maaakit/GTIA2DVI/doc/img/calib_1.png

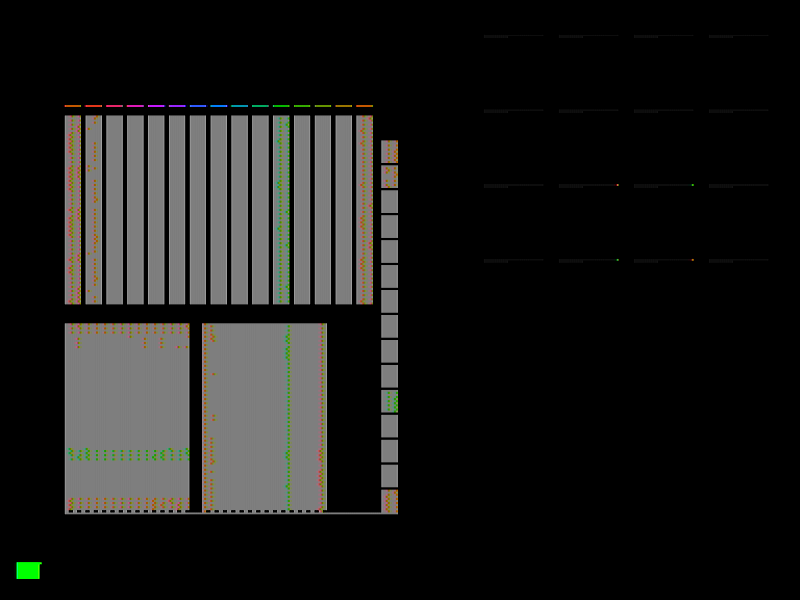
doc/img/calib_1.png
