maaakit/GTIA2DVI/software/gtia2dvi/gtia_palette.h

#include <stdlib.h>

#ifndef GTIA_PALETTE_H
#define GTIA_PALETTE_H

// PAL GTIA uses colors indexes 0-239 because color 15 is equal to color 1
// colors with indexes 240 to 255 are rgb colors used for example in menu screen

#define PALETTE_SIZE 256

#define BLACK 0
#define GRAY1 7
#define GRAY2 13
#define WHITE 15

#define RED 240
#define GREEN 241
#define BLUE 242
#define YELLOW 243
#define CYAN 244
#define MAGENTA 245

#define RED_D 246
#define GREEN_D 247
#define BLUE_D 248
#define YELLOW_D 249
#define CYAN_D 250
#define MAGENTA_D 251

#define RED_DD 252
#define GREEN_DD 253
#define BLUE_DD 254
#define YELLOW_DD 255

const uint32_t gtia_rgb888_palette[] = {
  // PAL GTIA colors
  0x00000000,  0x00111111,  0x00222222,  0x00333333,  0x00444444,  0x00555555,  0x00666666,  0x00777777,  0x00888888,  0x00999999,  0x00AAAAAA,  0x00BBBBBB,  0x00CCCCCC,  0x00DDDDDD,  0x00EEEEEE,  0x00FFFFFF,
  0x003F0000,  0x00500500,  0x00611600,  0x00722700,  0x00833800,  0x00944900,  0x00A55A01,  0x00B66B12,  0x00C77C23,  0x00D88D34,  0x00E99E45,  0x00FAAF56,  0x00FFC067,  0x00FFD178,  0x00FFE289,  0x00FFF39A,
  0x00500000,  0x00610000,  0x00720300,  0x00831403,  0x00942514,  0x00A53625,  0x00B64736,  0x00C75847,  0x00D86958,  0x00E97A69,  0x00FA8B7A,  0x00FF9C8B,  0x00FFAD9C,  0x00FFBEAD,  0x00FFCFBE,  0x00FFE0CF,
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
  // RGB colors
  0x00FF0000,  0x0000FF00,  0x000000FF,  0x00FFFF00,  0x0000FFFF,  0x00FF00FF,  0x00880000,  0x00008800,  0x00000088,  0x00888800,  0x00008888,  0x00880088,  0x00440000,  0x00004400,  0x00000044,  0x00444400,
};


#endif    
