maaakit/GTIA2DVI/software/gtia2dvi/tmds_table_256.h

#ifndef TMDS_TBL_256_H
#define TMDS_TBL_256_H


static const tmds_table_256[256] = {
    0x7fd00u,
    0x401ffu,
    0x405feu,
    0x7f901u,
    0x40dfcu,
    0x7f103u,
    0x7f502u,
    0x409fdu,
    0x41df8u,
    0x7e107u,
    0x7e506u,
    0x419f9u,
    0x7ed04u,
    0x411fbu,
    0x415fau,
    0x7e905u,
    0x43df0u,
    0x7c10fu,
    0x7c50eu,
    0x439f1u,
    0x7cd0cu,
    0x431f3u,
    0x435f2u,
    0x7c90du,
    0x7dd08u,
    0x421f7u,
    0x425f6u,
    0x7d909u,
    0x42df4u,
    0x7d10bu,
    0xa825fu,
    0x97ea0u,
    0x47de0u,
    0x7811fu,
    0x7851eu,
    0x479e1u,
    0x78d1cu,
    0x471e3u,
    0x475e2u,
    0x7891du,
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

};

#endif
