maaakit/GTIA2DVI/software/gtia2dvi/util/post_boot.h

#include "flash_storage.h"
#include "uart_log.h"

#ifndef POST_BOOT_H
#define POST_BOOT_H

enum PostBootAction
{
    FACTORY_RESET = (1 << 0),
    WRITE_PRESET = (1 << 1),
    WRITE_CONFIG = (1 << 2)
};

enum PostBootAction post_boot_action __attribute__((section(".uninitialized_data")));

uint32_t checksum __attribute__((section(".uninitialized_data")));

uint32_t calculate_checksum()
{
    return 999 - post_boot_action;
}

void set_post_boot_action(enum PostBootAction action)
{
    post_boot_action |= action;
    checksum = calculate_checksum();
}

void exec_post_boot_action()
{
    if (checksum != calculate_checksum())
    {
        sprintf(buf, "  skipping! checksum not match %X!=%X", checksum, calculate_checksum());
        uart_log_putln(buf);
        return;
    }

    if (watchdog_caused_reboot() == false)
    {
        post_boot_action = 0;
        return;
    }

    uart_log_putln("executing post boot actions:");

    if (post_boot_action == 0)
    {
        uart_log_putln("  nothing requested");
        return;
    }

    if (post_boot_action & FACTORY_RESET)
    {
        flash_factory_reset();
        uart_log_putln("  factory reset - done");
    }

    if (post_boot_action & WRITE_PRESET)
    {
        flash_save_preset((uint8_t *)&calibration_data);
        uart_log_putln("  calibration data - saved");
    }

    if (post_boot_action & WRITE_CONFIG)
    {
        flash_save_config(&app_cfg);
        uart_log_putln("  config data - saved");
    }

    post_boot_action = 0;
}

#endif
